timonsku/RGB-Ring-Light-Hack/Case-Modification-Reference/2021-03-09-2893.jpg

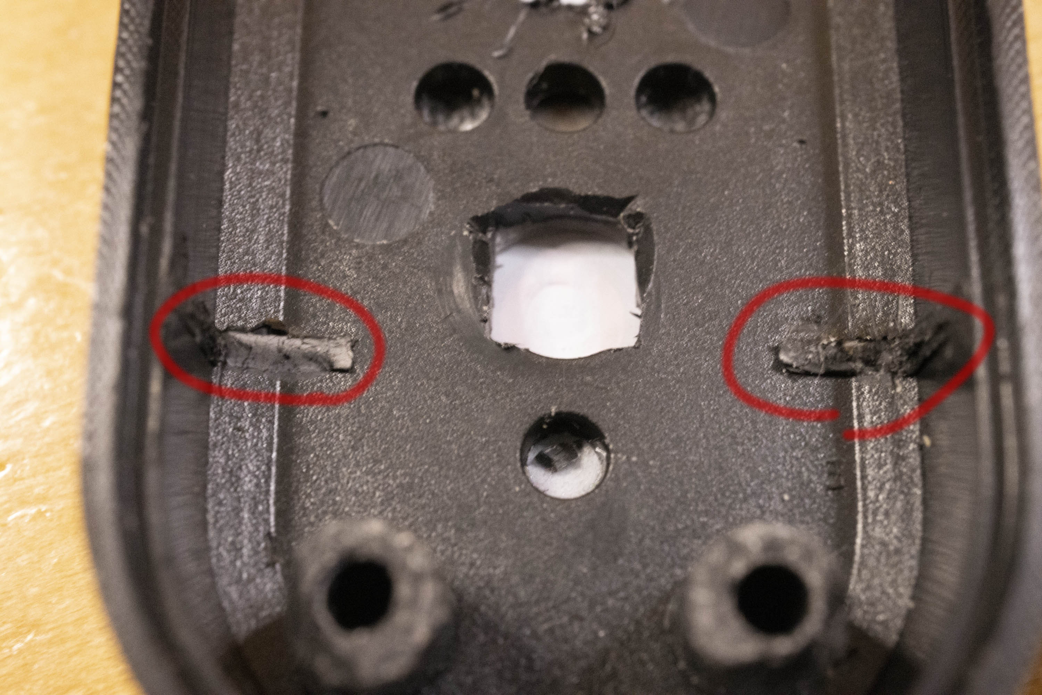
Case-Modification-Reference/2021-03-09-2893.jpg
