timonsku/RGB-Ring-Light-Hack/Case-Hack-PCB/solder-reference-headers.jpg

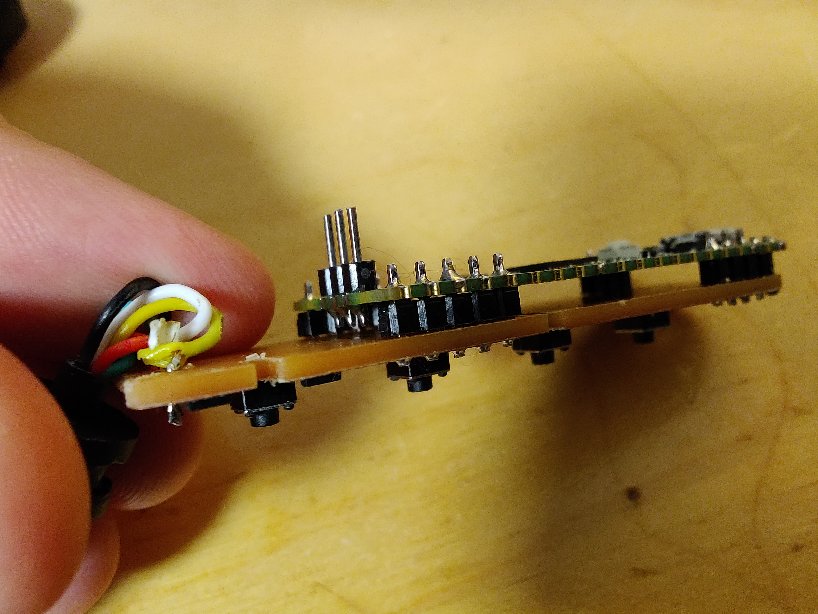
Case-Hack-PCB/solder-reference-headers.jpg
